StaRky33/ZigbeeMacropad/Pictures/nanoESP32-C6.jpg

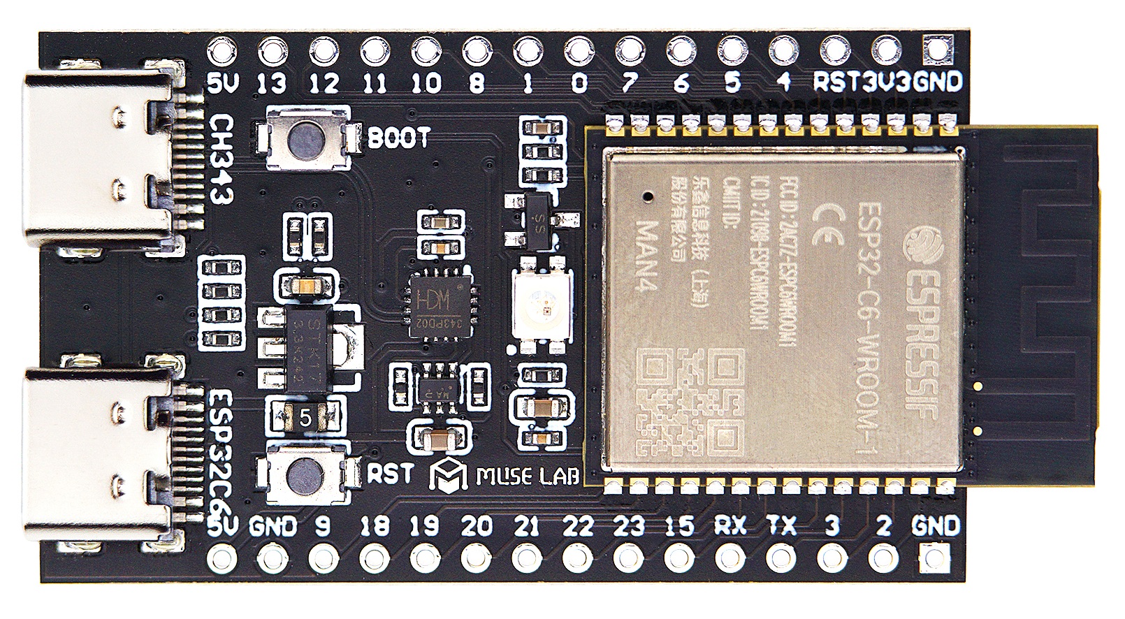
Pictures/nanoESP32-C6.jpg
