StaRky33/ZigbeeMacropad/Pictures/OnOffSwitch.jpg

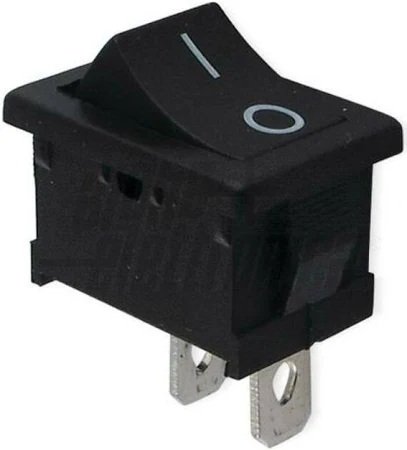
Pictures/OnOffSwitch.jpg
