StaRky33/ZigbeeMacropad/Pictures/PXL_20251210_093622129.jpg

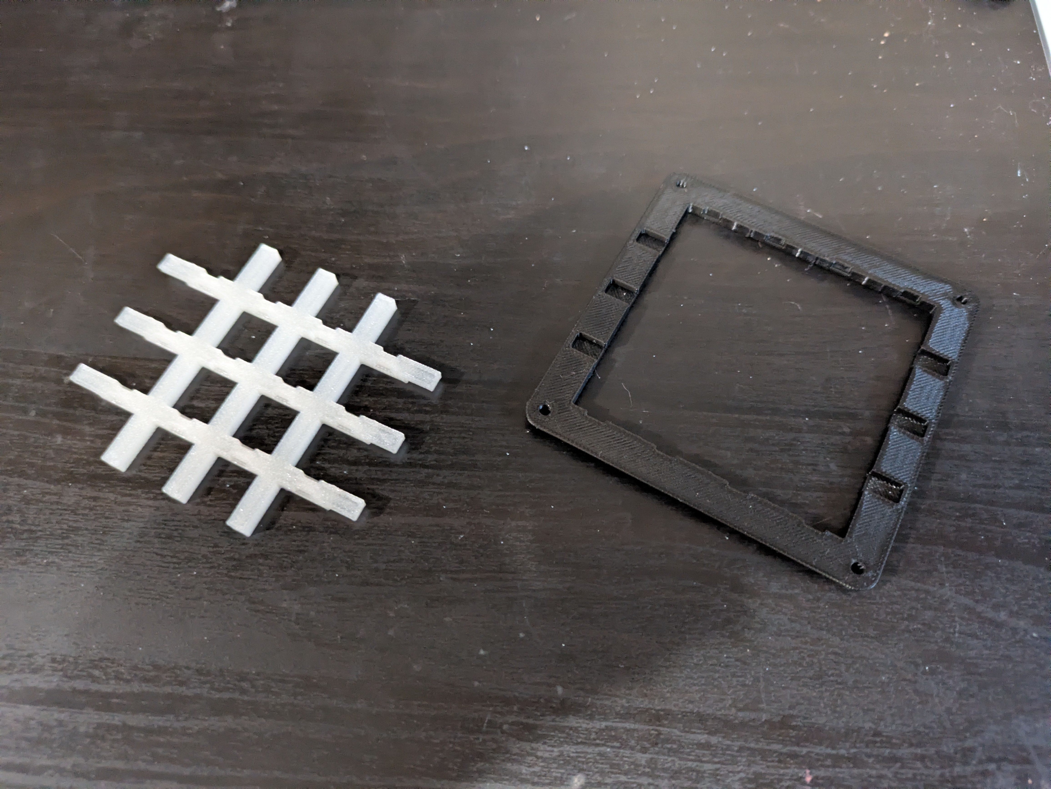
Pictures/PXL_20251210_093622129.jpg
