StaRky33/ZigbeeMacropad/Pictures/PXL_20251212_120037829.jpg

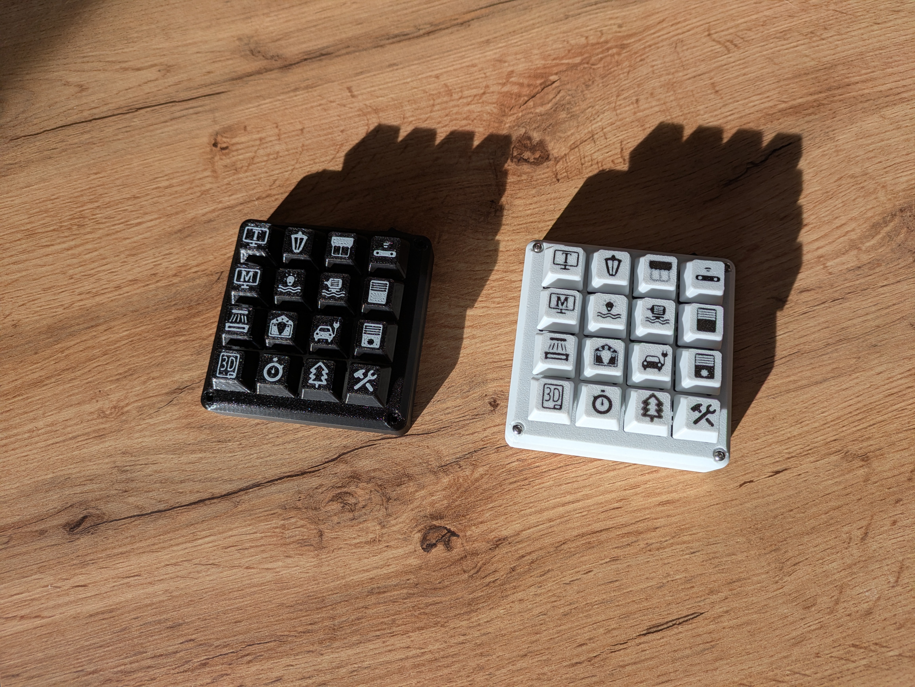
Pictures/PXL_20251212_120037829.jpg
