StaRky33/ZigbeeMacropad/Pictures/PXL_20251212_120048397.jpg

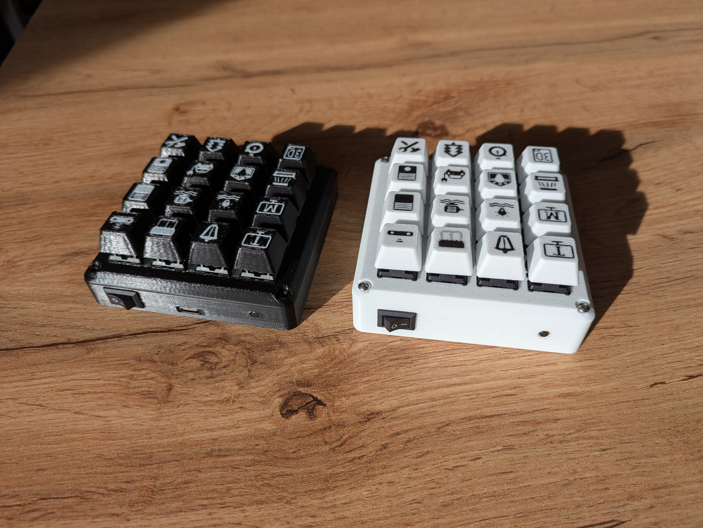
Pictures/PXL_20251212_120048397.jpg
