StaRky33/ZigbeeMacropad/Pictures/PXL_20251215_120037287.jpg

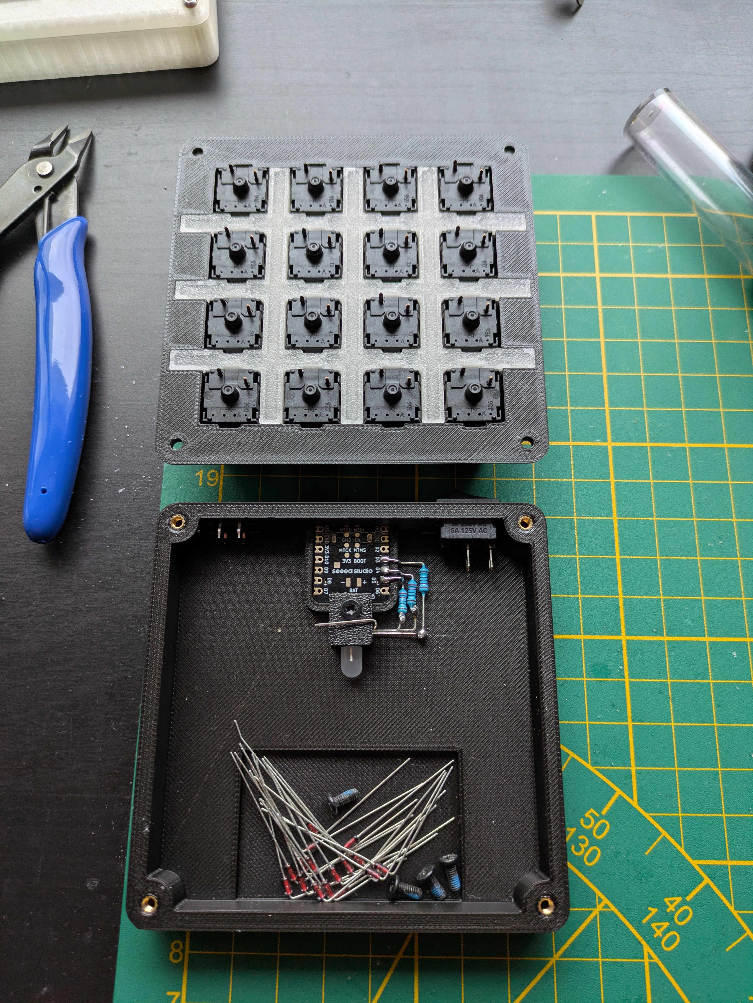
Pictures/PXL_20251215_120037287.jpg
