StaRky33/ZigbeeMacropad/Pictures/PXL_20251217_133015329.jpg

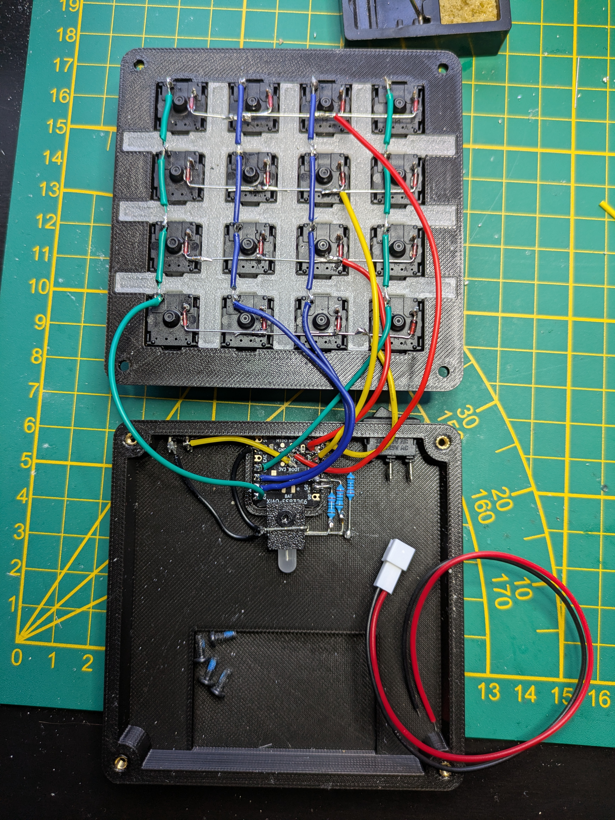
Pictures/PXL_20251217_133015329.jpg
