StaRky33/ZigbeeMacropad/Pictures/PXL_20251217_133022534.jpg

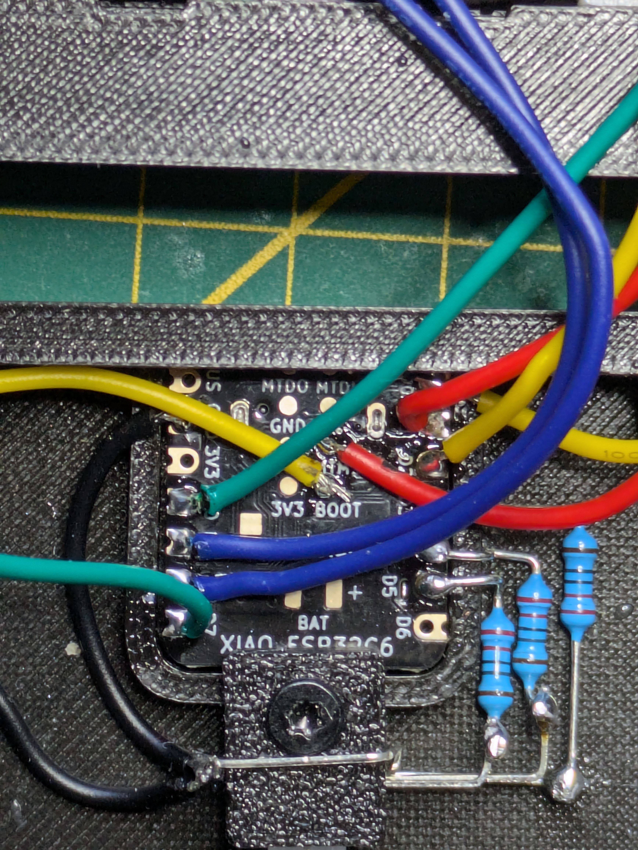
Pictures/PXL_20251217_133022534.jpg
