StaRky33/ZigbeeMacropad/Pictures/PXL_20260106_132515787.jpg

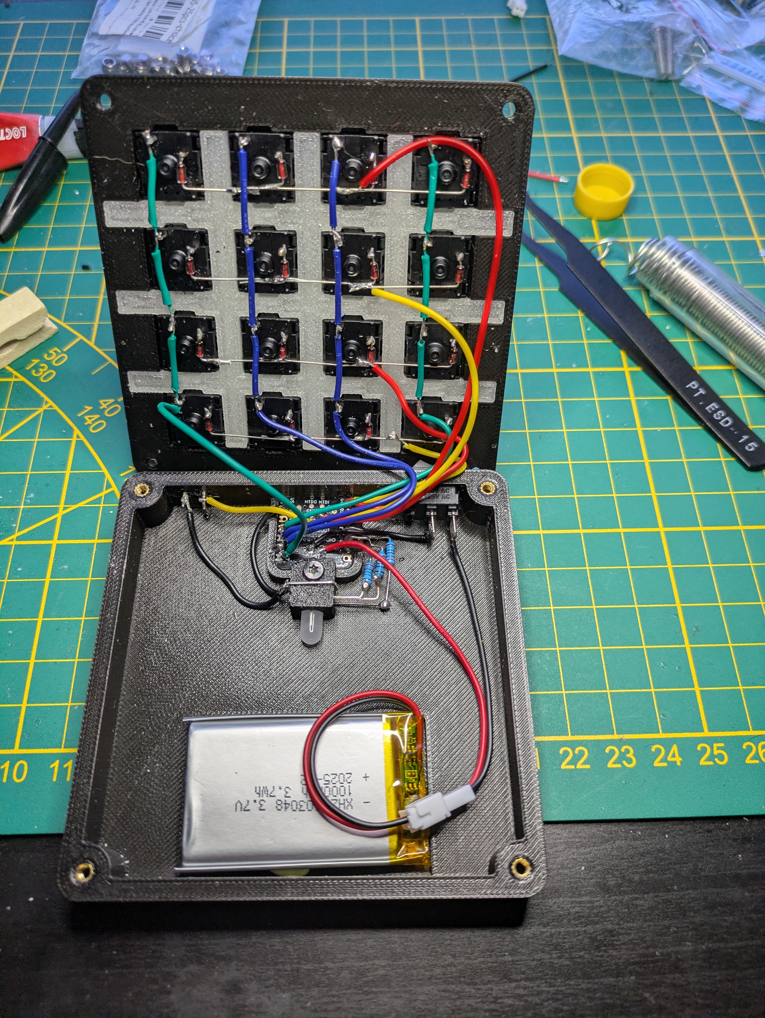
Pictures/PXL_20260106_132515787.jpg
