StaRky33/ZigbeeMacropad/Pictures/PXL_20260106_132522850.jpg

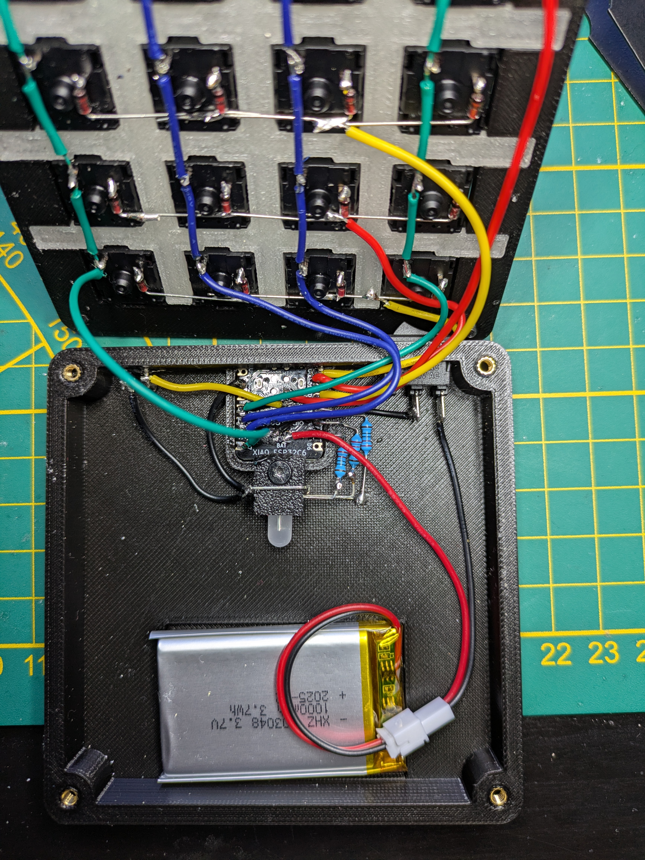
Pictures/PXL_20260106_132522850.jpg
