StaRky33/ZigbeeMacropad/Pictures/PXL_20260119_161722353.jpg

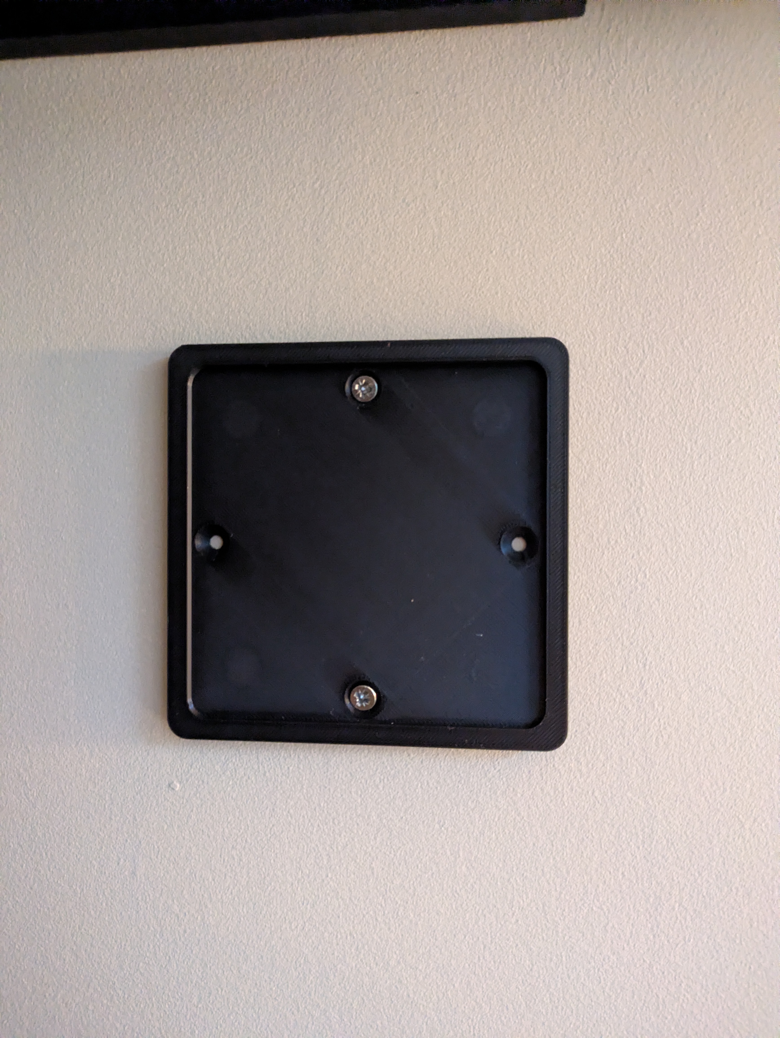
Pictures/PXL_20260119_161722353.jpg
