StaRky33/ZigbeeMacropad/Pictures/PXL_20260119_161728571.jpg

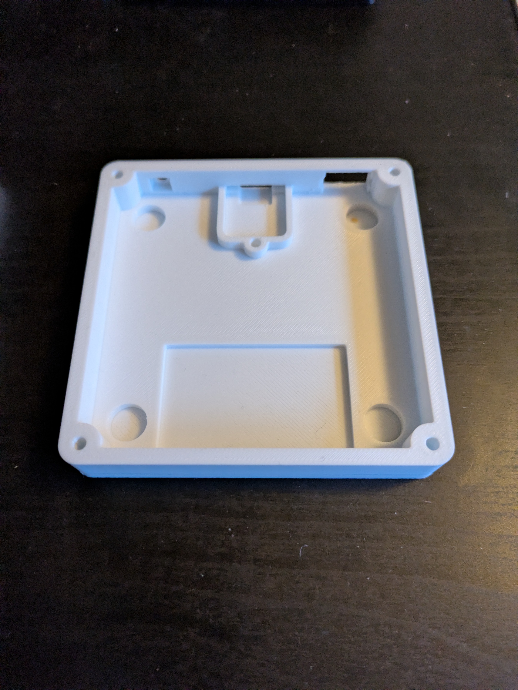
Pictures/PXL_20260119_161728571.jpg
