StaRky33/ZigbeeMacropad/Pictures/PXL_20260119_161735684.jpg

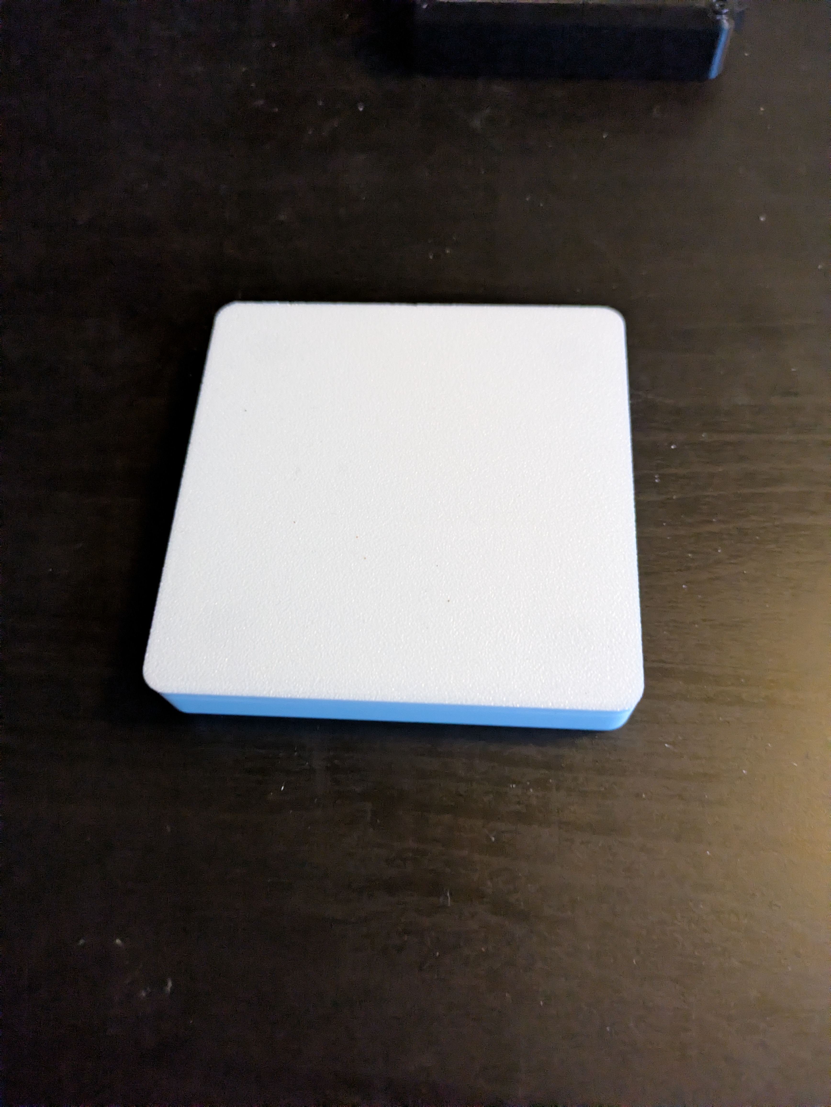
Pictures/PXL_20260119_161735684.jpg
