StaRky33/ZigbeeMacropad/Pictures/PXL_20260119_161747687.jpg

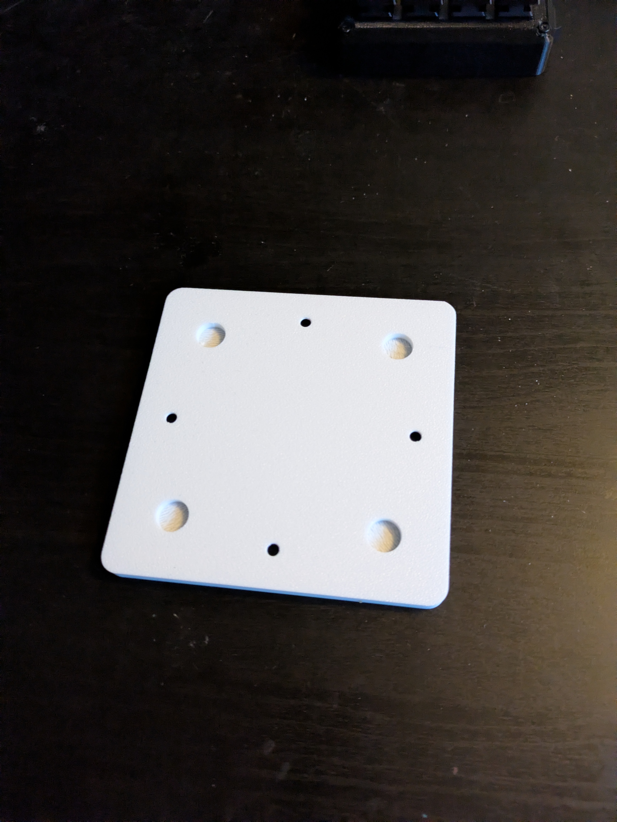
Pictures/PXL_20260119_161747687.jpg
