StaRky33/ZigbeeMacropad/Pictures/PXL_20260119_161750838.jpg

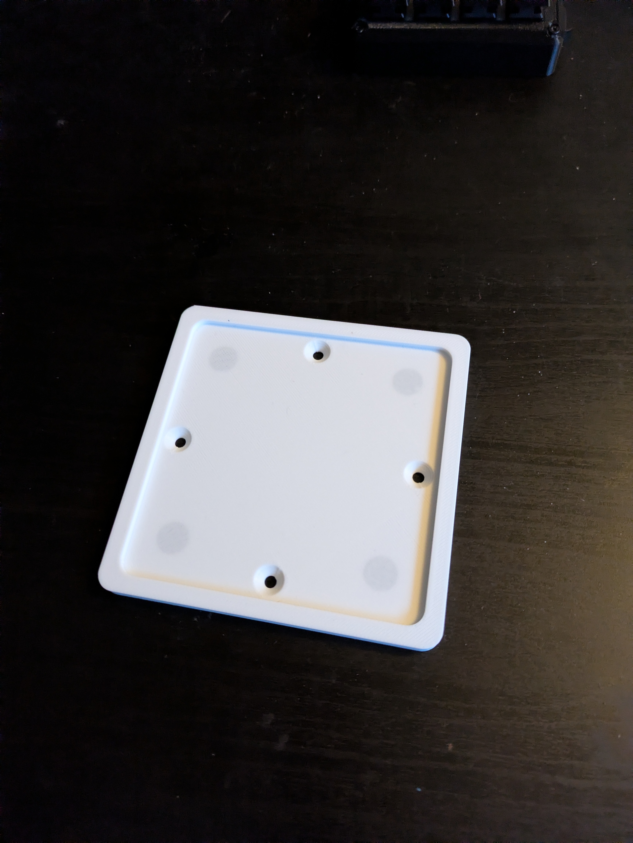
Pictures/PXL_20260119_161750838.jpg
