StaRky33/ZigbeeMacropad/Pictures/PXL_20260408_143943503.jpg

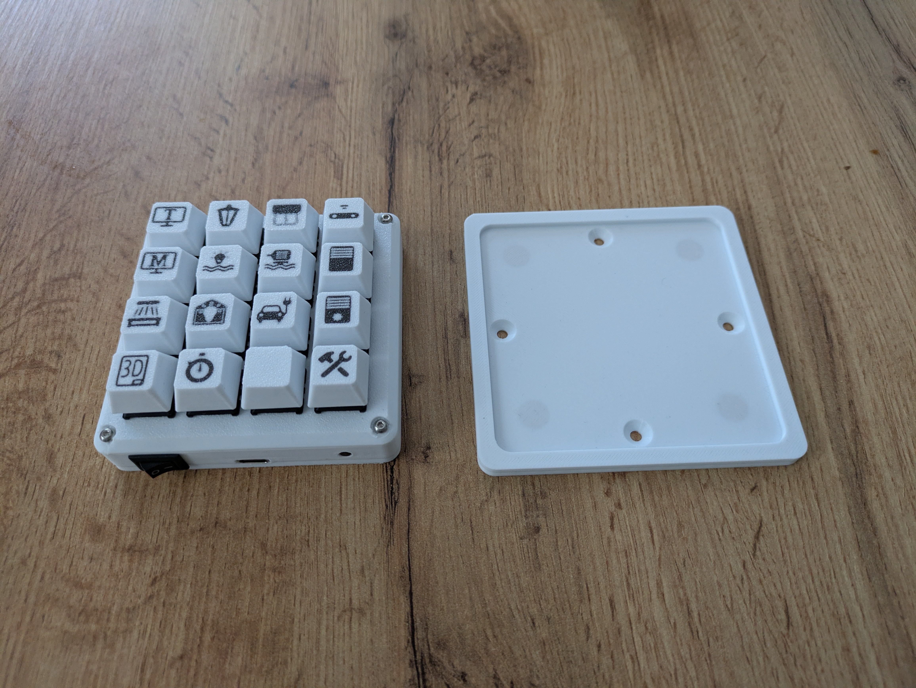
Pictures/PXL_20260408_143943503.jpg
