StaRky33/ZigbeeMacropad/Pictures/PXL_20260408_143949903.jpg

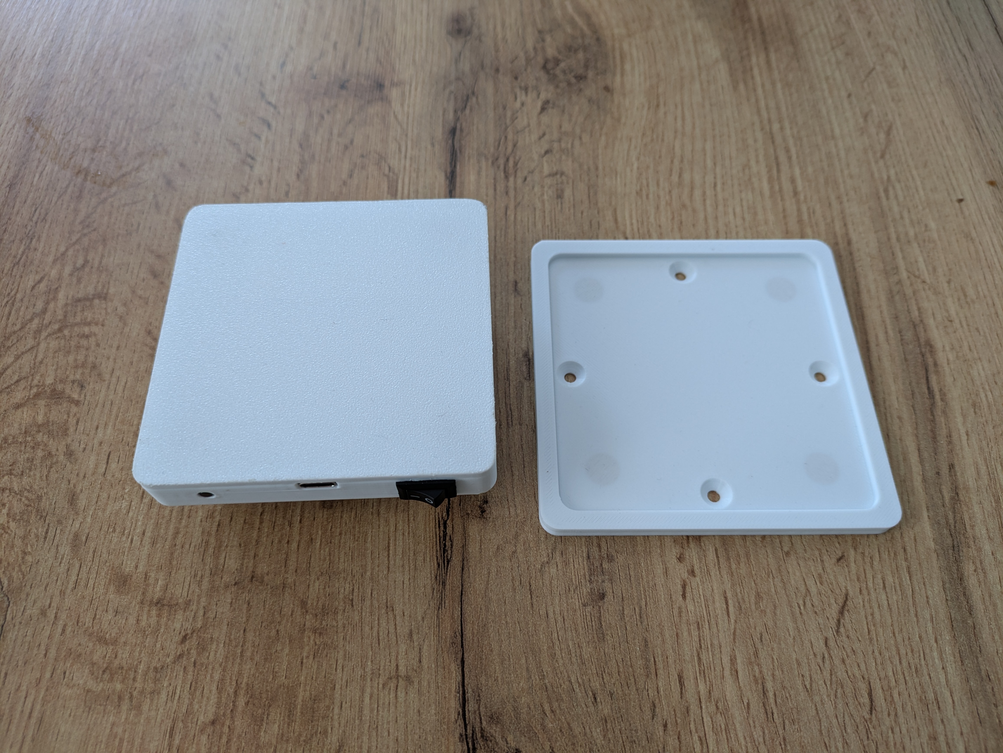
Pictures/PXL_20260408_143949903.jpg
