StaRky33/ZigbeeMacropad/Pictures/PXL_20260408_144051718.jpg

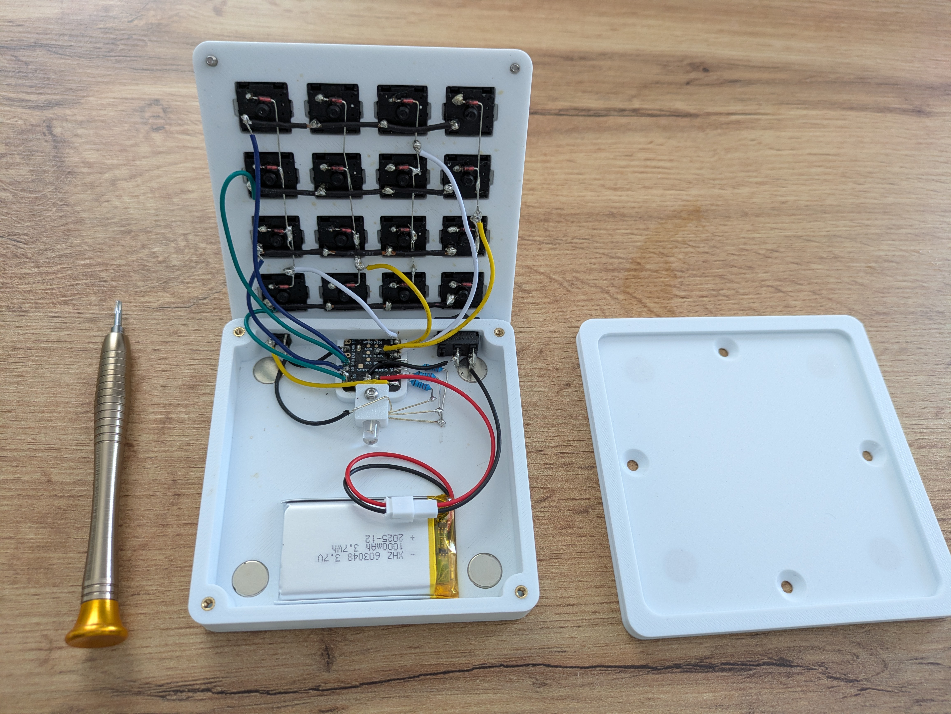
Pictures/PXL_20260408_144051718.jpg
