StaRky33/ZigbeeMacropad/Pictures/PXL_20260408_144057199.jpg

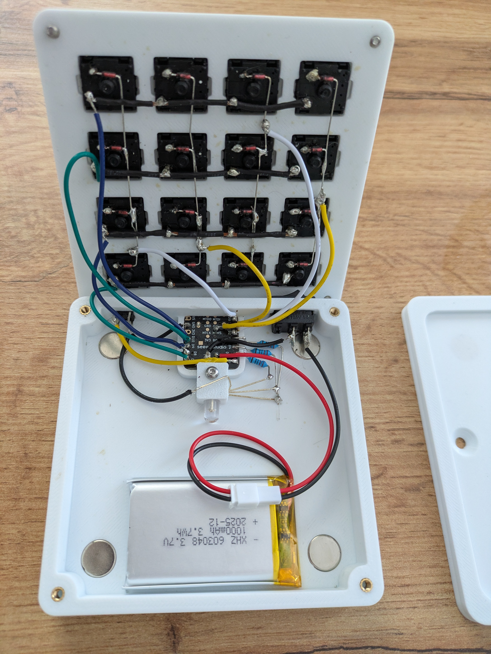
Pictures/PXL_20260408_144057199.jpg
